medo64/PowerFEC/firmware/io.c

#include <xc.h>
#include <stdbool.h>
#include <stdint.h>
#include "app.h"
#include "io.h"

#if defined(BOARD_REV_A)
    #include "adc.h"
#include "Microchip/usb_device.h"
#endif

void io_init(void) {
    // Out: LED1 (left)
#if defined(BOARD_REV_A)
    LATCbits.LATC5 = 0;
    TRISCbits.TRISC5 = 0;  // default state is off (inverse)
#else
    LATCbits.LATC5 = 0;
    TRISCbits.TRISC5 = 0;  // default state is off (inverse)
#endif

    // Out: LED2 (right)
    LATCbits.LATC2 = 0;    // default state is off
    TRISCbits.TRISC2 = 0;
    ANSELCbits.ANSC2 = 0;

    // Out: POWER_EN#
    LATCbits.LATC4 = 0;
    TRISCbits.TRISC4 = 0;  // default state is on

    // In: FAULT#
#if !defined(BOARD_REV_A)
    WPUAbits.WPUA5 = 1;    // weak pull-up enabled
    LATAbits.LATA5 = 0;
    TRISAbits.TRISA5 = 1;  // input
#endif
}

#if defined(BOARD_REV_A)
bool in_isFaulted(void) {
    if (!out_power_isEnabled()) { return false; }  // not a fault if it's disabled
    uint16_t voltage = adc_getVoltage();
    return (voltage <= 5);  // small enough not to cause false positives
}
#endif
